whowechina/ju_pico/Production/3DPrint/ju_pico+_button_seat_55.6mm.stl

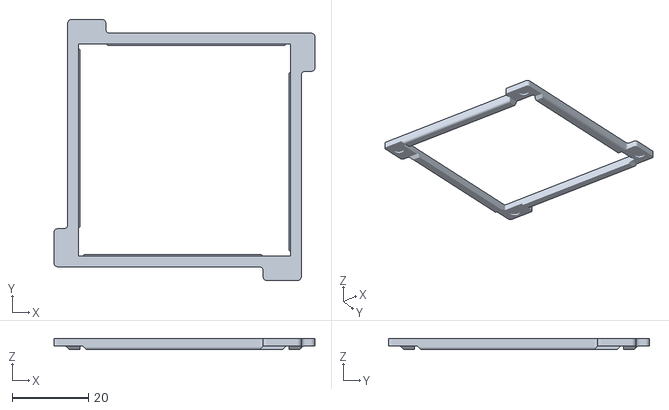
[picture p31: CAD file, 2026-01-03]
Production/3DPrint/ju_pico+_button_seat_55.6mm.stl
68.4 x 68.4 x 3.00
