whowechina/ju_pico/Production/CNC/ju_pico_cnc_banner.step

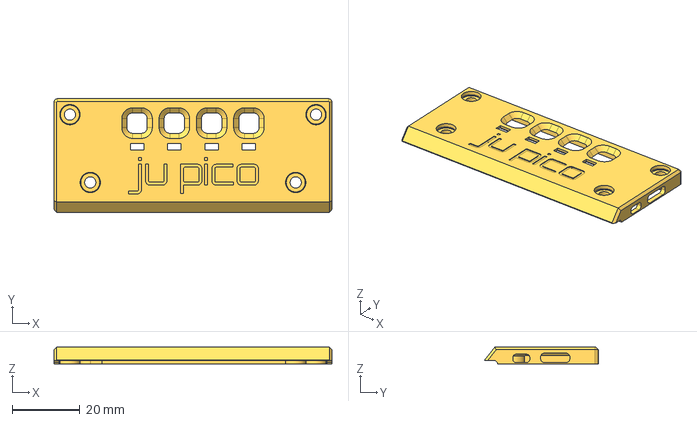
[picture p32: CAD file, 2024-12-04]
Production/CNC/ju_pico_cnc_banner.step
82.0 x 33.5 x 5.00 mm
