whowechina/ju_pico/PCB/Touch/3dmodels/Kailh LP Choc PC Keycap.step

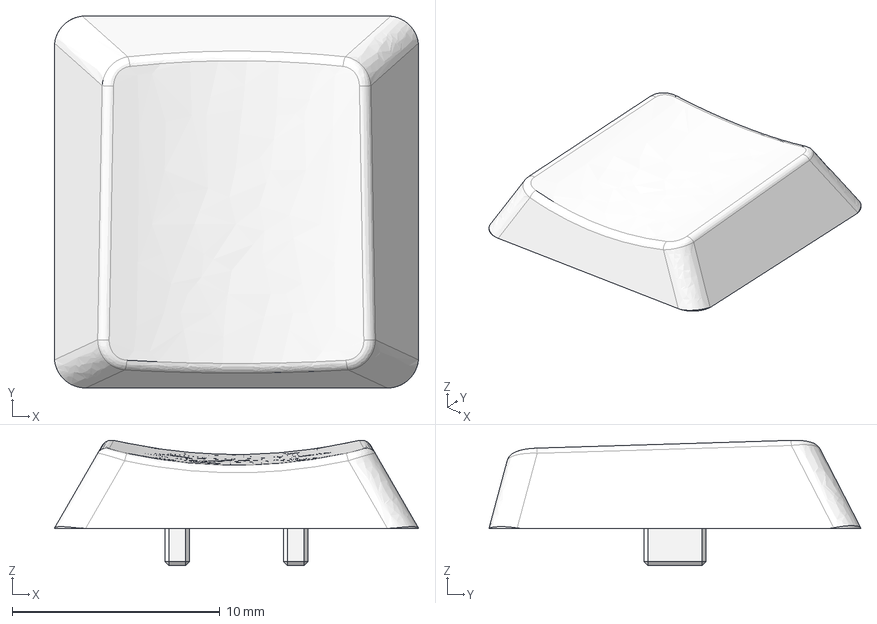
[picture p33: CAD file, 2024-10-23]
PCB/Touch/3dmodels/Kailh LP Choc PC Keycap.step
17.5 x 17.9 x 6.03 mm
