whowechina/ju_pico/PCB/Touch/3dmodels/User Library-WS2812-4020.step

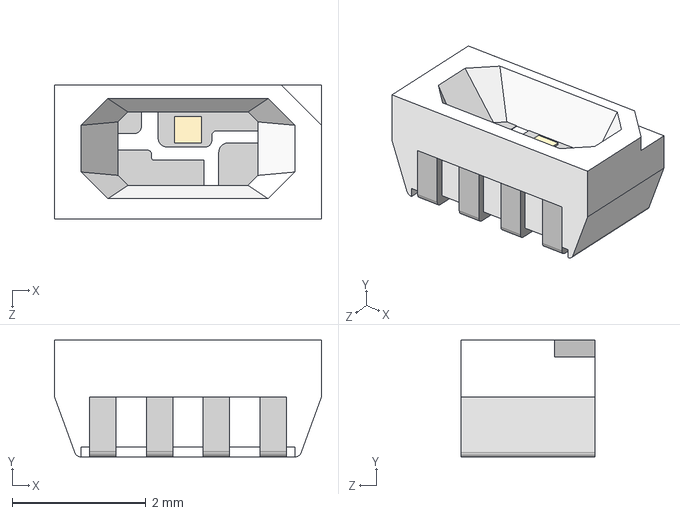
[picture p34: CAD file, 2024-10-23]
PCB/Touch/3dmodels/User Library-WS2812-4020.step
4.00 x 1.75 x 2.00 mm
