whowechina/ju_pico/PCB/Touch/3dmodels/Magnetic Pogo Connector 5 Pin (Type 4).STEP

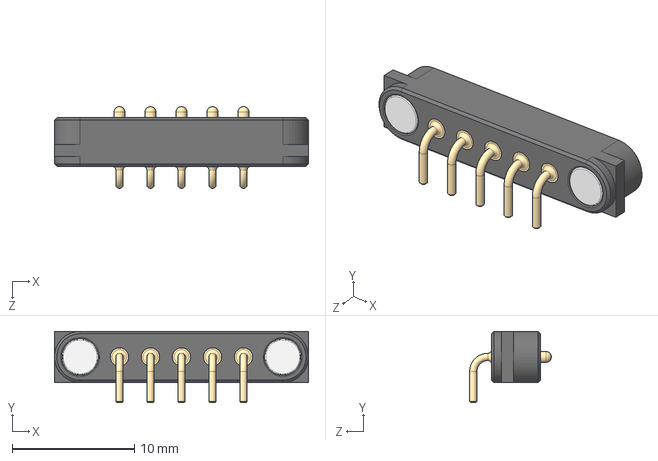
[picture p35: CAD file, 2024-10-23]
PCB/Touch/3dmodels/Magnetic Pogo Connector 5 Pin (Type 4).STEP
20.8 x 5.85 x 6.70 mm
