whowechina/ju_pico/PCB/Touch/3dmodels/Tact Switch 4.5mm SMT.step

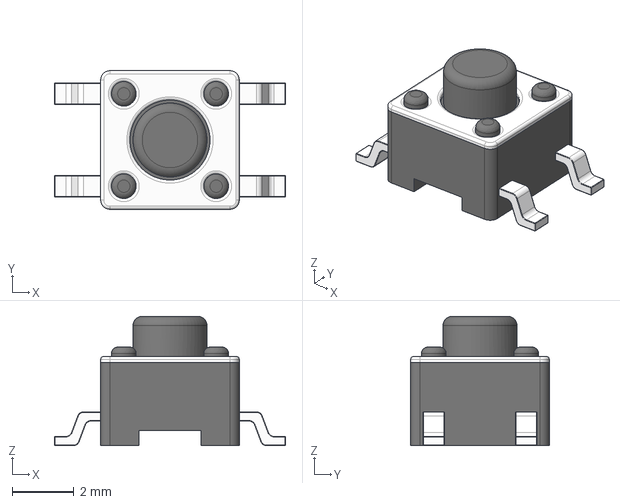
[picture p36: CAD file, 2024-10-23]
PCB/Touch/3dmodels/Tact Switch 4.5mm SMT.step
7.50 x 4.50 x 4.20 mm
