whowechina/ju_pico/PCB/Touch/3dmodels/User Library-pj-393-8.STEP

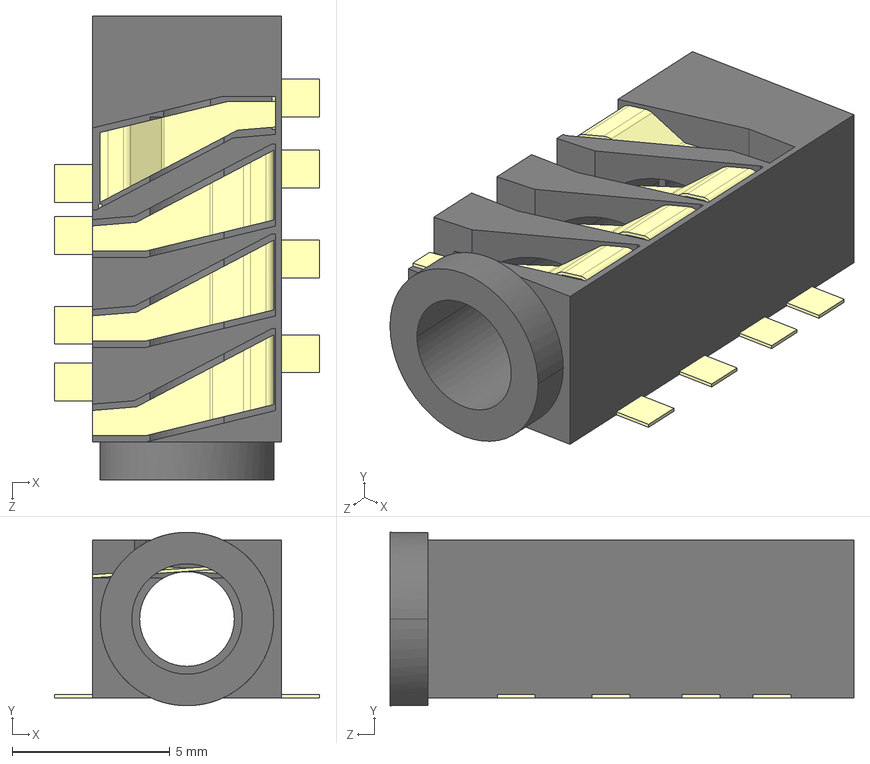
[picture p37: CAD file, 2024-10-23]
PCB/Touch/3dmodels/User Library-pj-393-8.STEP
8.40 x 5.50 x 14.7 mm
PJ-393-8_1
PJ-393-8_2 x 4
PJ-393-8_3
PJ-393-8_4 x 3
