whowechina/ju_pico/Production/3DPrint/ju_pico+_banner.3mf

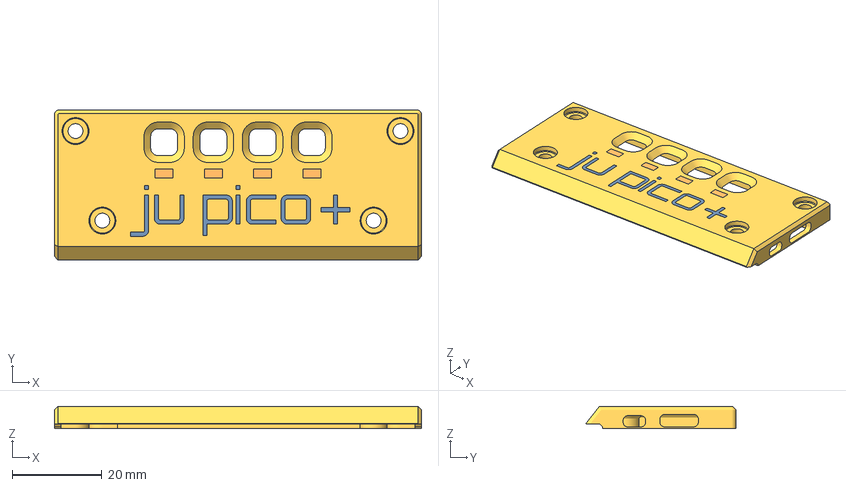
[picture p38: CAD file, 2026-01-03]
Production/3DPrint/ju_pico+_banner.3mf
82.0 x 33.5 x 5.00 mm
Banner
Logo_1
Logo_2
Logo_3
Logo_4
Logo_5
Logo_6
Logo_7
Logo_8
Logo_9
LED_1
LED_2
LED_3
LED_4
