whowechina/ju_pico/PCB/Touch/3dmodels/WS2812-2020.STEP

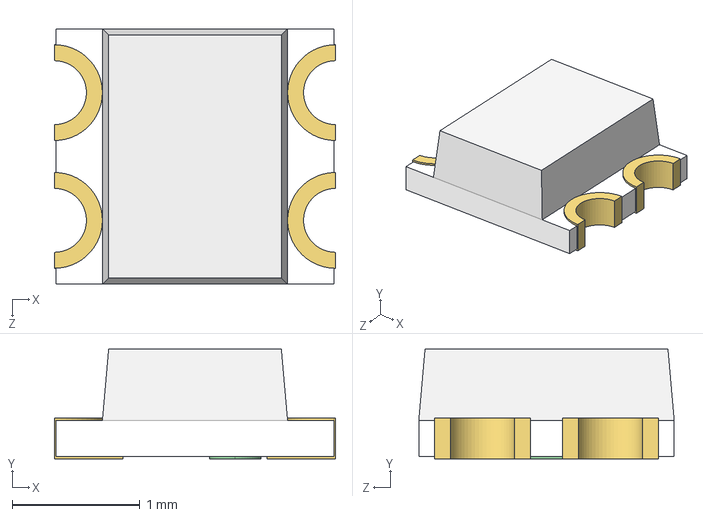
[picture p39: CAD file, 2024-10-23]
PCB/Touch/3dmodels/WS2812-2020.STEP
2.20 x 0.86 x 2.00 mm
