whowechina/ju_pico/Production/3DPrint/ju_pico_led_diffuser_for_cnc.stl

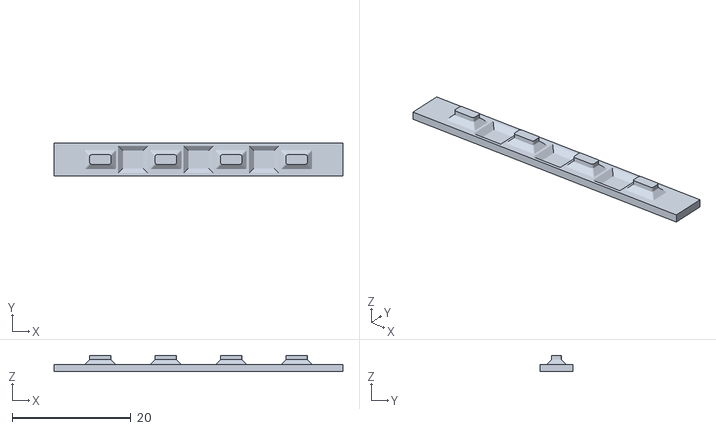
[picture p40: CAD file, 2024-12-06]
Production/3DPrint/ju_pico_led_diffuser_for_cnc.stl
48.6 x 5.60 x 2.70
