whowechina/ju_pico/PCB/Touch/3dmodels/User Library-WS2812-2020.step

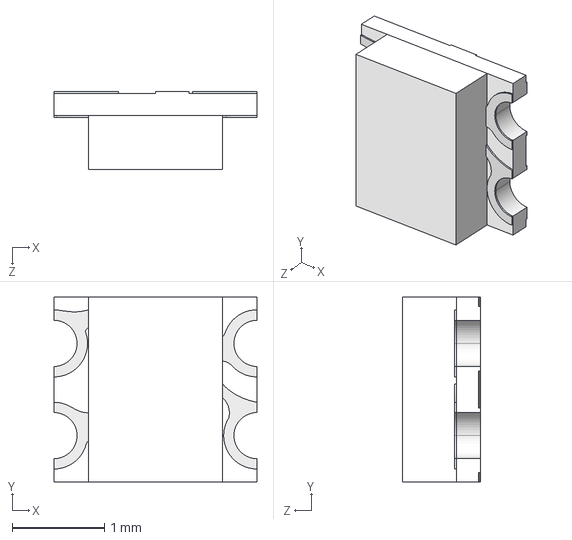
[picture p41: CAD file, 2024-10-23]
PCB/Touch/3dmodels/User Library-WS2812-2020.step
2.20 x 2.00 x 0.84 mm
