whowechina/ju_pico/Production/3DPrint/ju_pico_frame_hexnut.stl

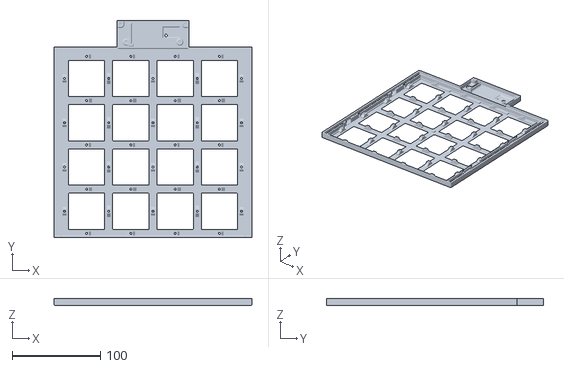
[picture p42: CAD file, 2024-12-04]
Production/3DPrint/ju_pico_frame_hexnut.stl
224.0 x 246.0 x 8.20
