whowechina/ju_pico/PCB/Touch/3dmodels/User Library-PTS645SL95SMTR92-LFS.STEP

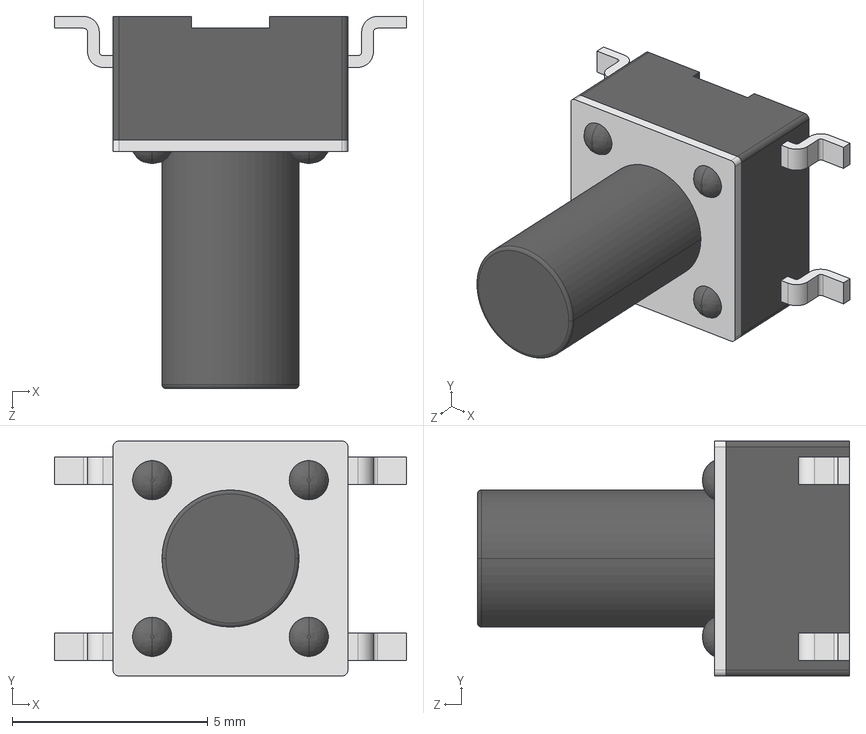
[picture p43: CAD file, 2024-10-23]
PCB/Touch/3dmodels/User Library-PTS645SL95SMTR92-LFS.STEP
9.00 x 6.00 x 9.50 mm
