whowechina/ju_pico/Production/3DPrint/ju_pico_button_seat_39.8mm.stl

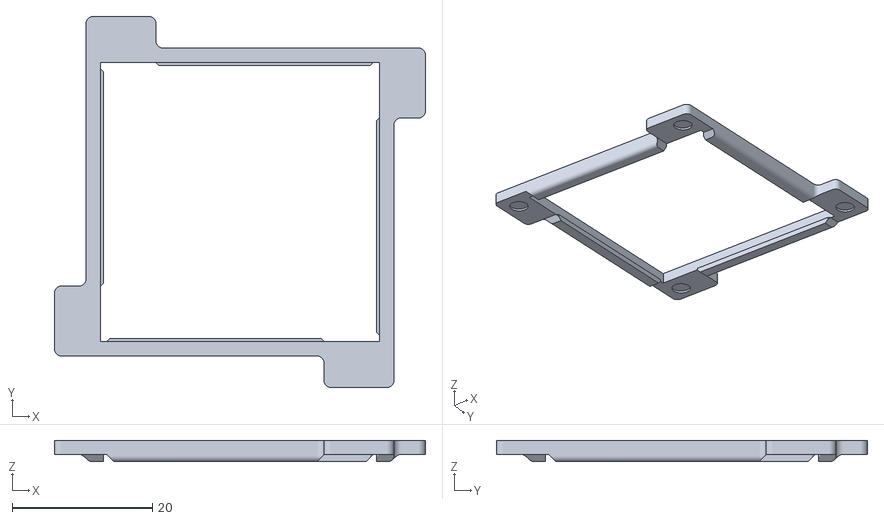
[picture p44: CAD file, 2024-11-11]
Production/3DPrint/ju_pico_button_seat_39.8mm.stl
53.0 x 53.0 x 3.00
