whowechina/ju_pico/PCB/Touch/3dmodels/mpr121_breakout_v13.stl

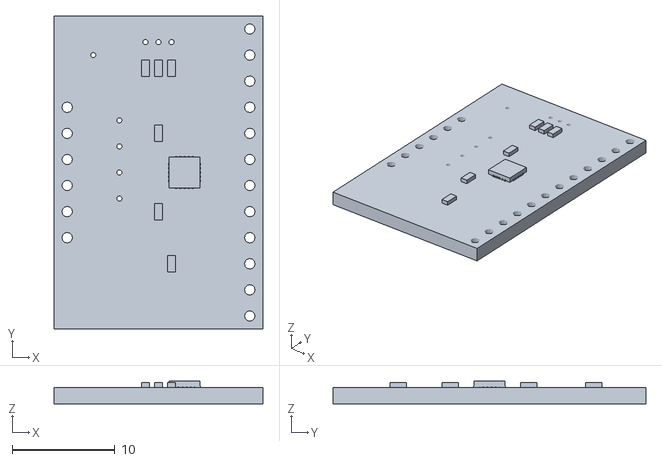
[picture p45: CAD file, 2024-10-23]
PCB/Touch/3dmodels/mpr121_breakout_v13.stl
20.3 x 30.5 x 2.20
