whowechina/ju_pico/PCB/Touch/3dmodels/SW_Kailh_Choc_V1.stp

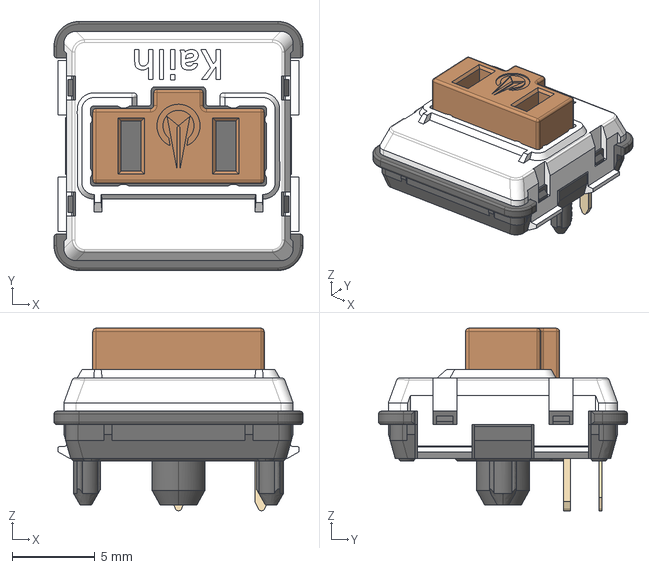
[picture p46: CAD file, 2024-10-23]
PCB/Touch/3dmodels/SW_Kailh_Choc_V1.stp
15.0 x 15.0 x 11.0 mm
