whowechina/ju_pico/PCB/Touch/3dmodels/WS2812B.step

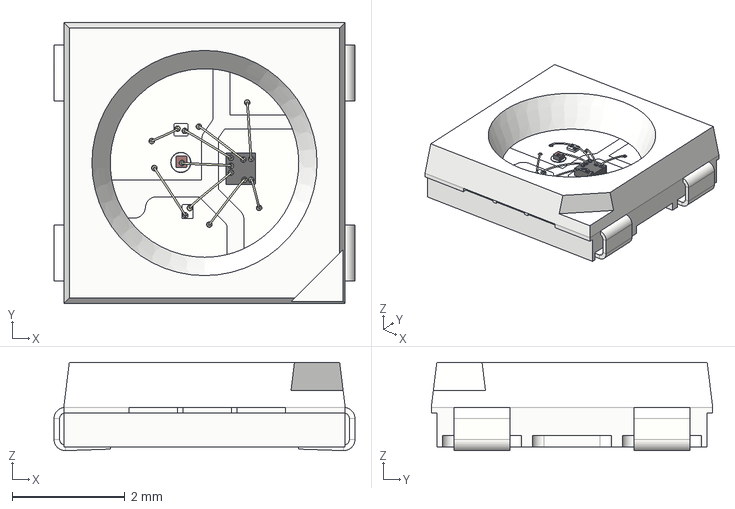
[picture p47: CAD file, 2024-10-23]
PCB/Touch/3dmodels/WS2812B.step
5.35 x 5.00 x 1.57 mm
