whowechina/ju_pico/PCB/Touch/3dmodels/Magnetic Pogo Connector 5 Pin (Type 3).STEP

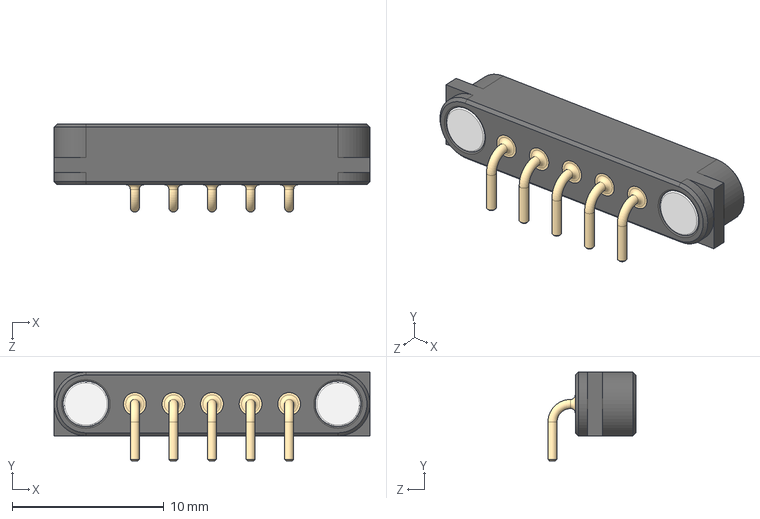
[picture p48: CAD file, 2024-10-23]
PCB/Touch/3dmodels/Magnetic Pogo Connector 5 Pin (Type 3).STEP
20.8 x 5.85 x 5.80 mm
