whowechina/ju_pico/PCB/Touch/3dmodels/EVQ-P1D05M.stp

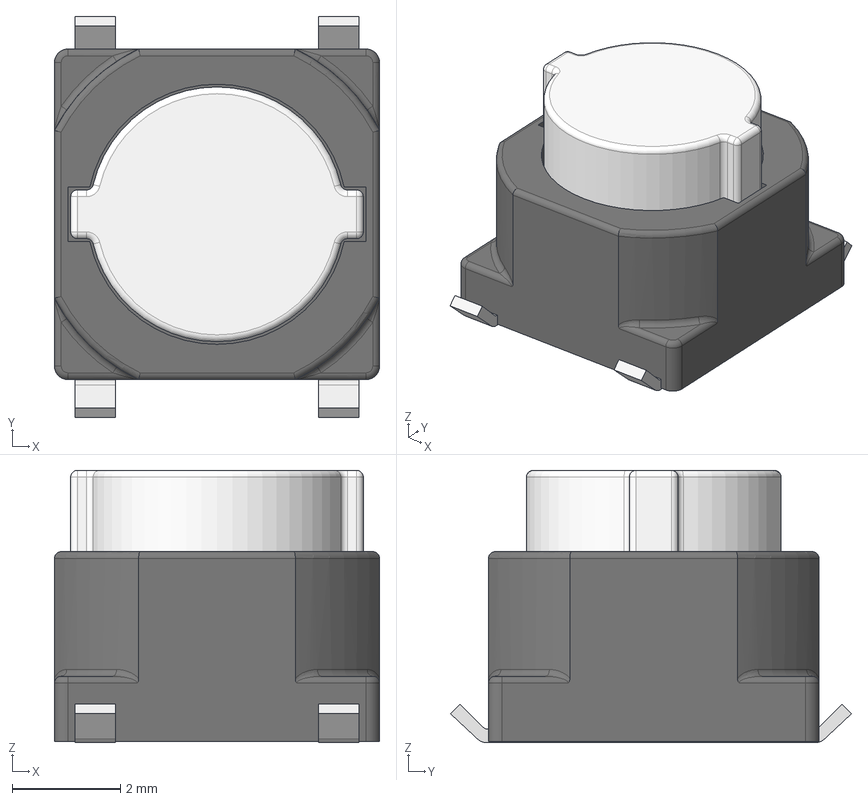
[picture p49: CAD file, 2024-10-23]
PCB/Touch/3dmodels/EVQ-P1D05M.stp
6.00 x 7.40 x 5.03 mm
