whowechina/ju_pico/PCB/Touch/3dmodels/SW_Hotswap_Kailh_MX.stp

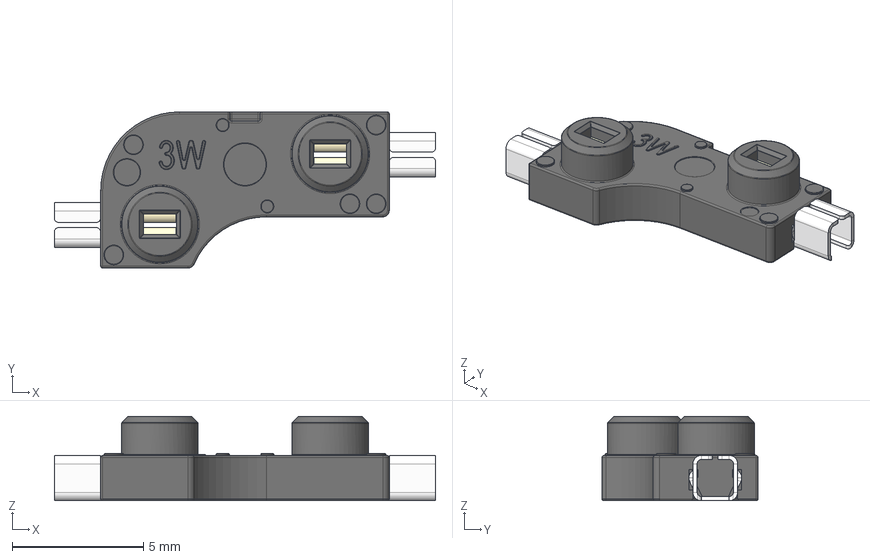
[picture p50: CAD file, 2024-10-23]
PCB/Touch/3dmodels/SW_Hotswap_Kailh_MX.stp
14.5 x 5.95 x 3.22 mm
