whowechina/ju_pico/PCB/Touch/3dmodels/SW_Hotswap_Kailh_Choc_V1.stp

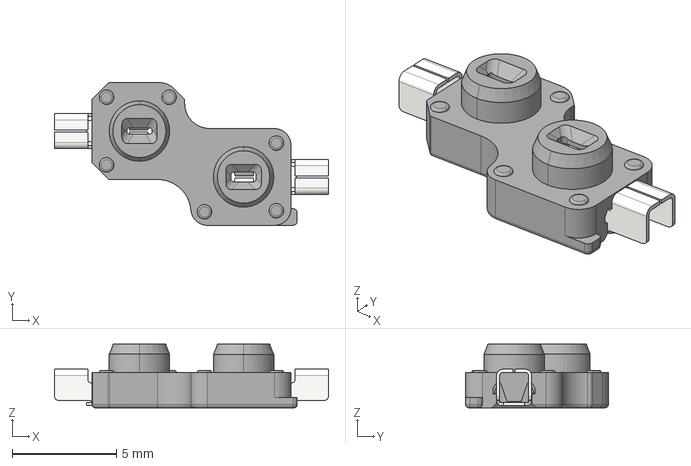
[picture p51: CAD file, 2024-10-23]
PCB/Touch/3dmodels/SW_Hotswap_Kailh_Choc_V1.stp
13.2 x 6.85 x 3.05 mm
