whowechina/ju_pico/PCB/Touch/3dmodels/WS2812-0807.STEP

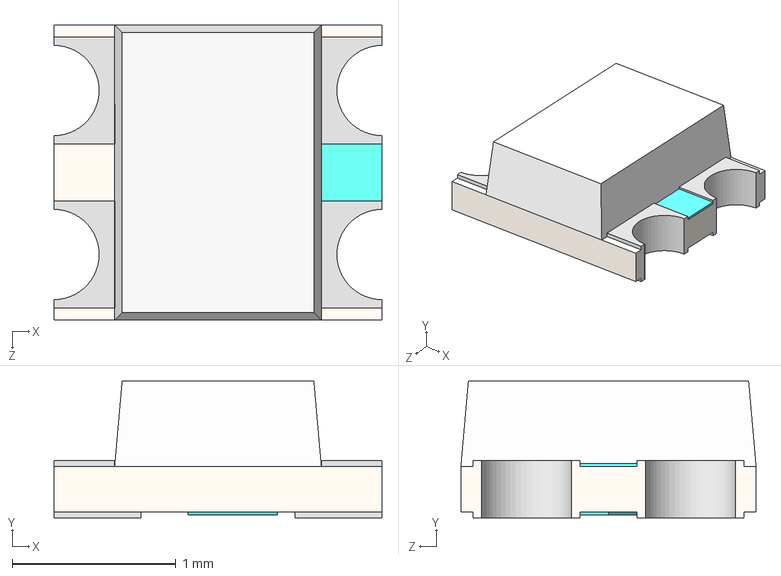
[picture p52: CAD file, 2024-10-23]
PCB/Touch/3dmodels/WS2812-0807.STEP
2.00 x 0.835 x 1.80 mm
