whowechina/ju_pico/PCB/Touch/3dmodels/Magnetic Pogo Connector 5 Pin (Type 1).STEP

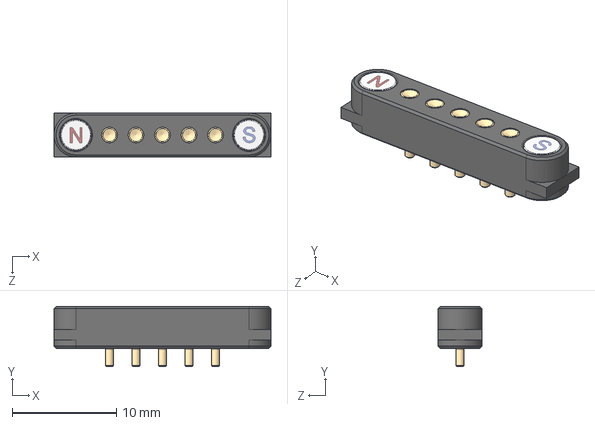
[picture p53: CAD file, 2024-10-23]
PCB/Touch/3dmodels/Magnetic Pogo Connector 5 Pin (Type 1).STEP
20.8 x 5.75 x 4.20 mm
