whowechina/ju_pico/PCB/Touch/3dmodels/SMD WS2812B-3535.step

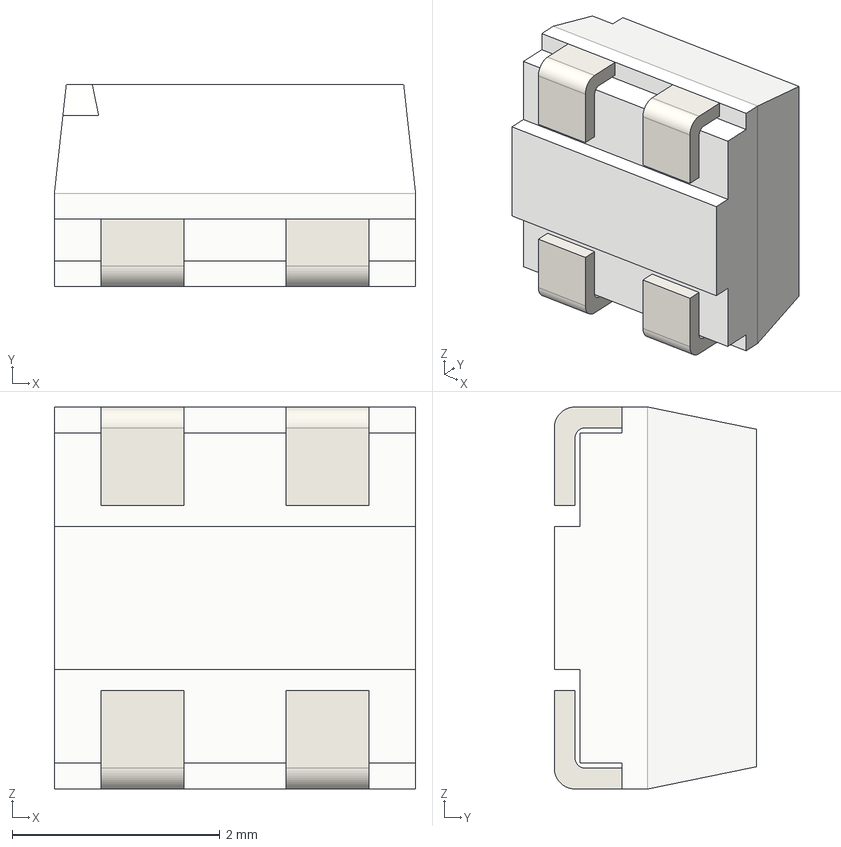
[picture p54: CAD file, 2024-10-23]
PCB/Touch/3dmodels/SMD WS2812B-3535.step
3.48 x 1.95 x 3.68 mm
