whowechina/ju_pico/PCB/Touch/3dmodels/SKPMAM.STEP

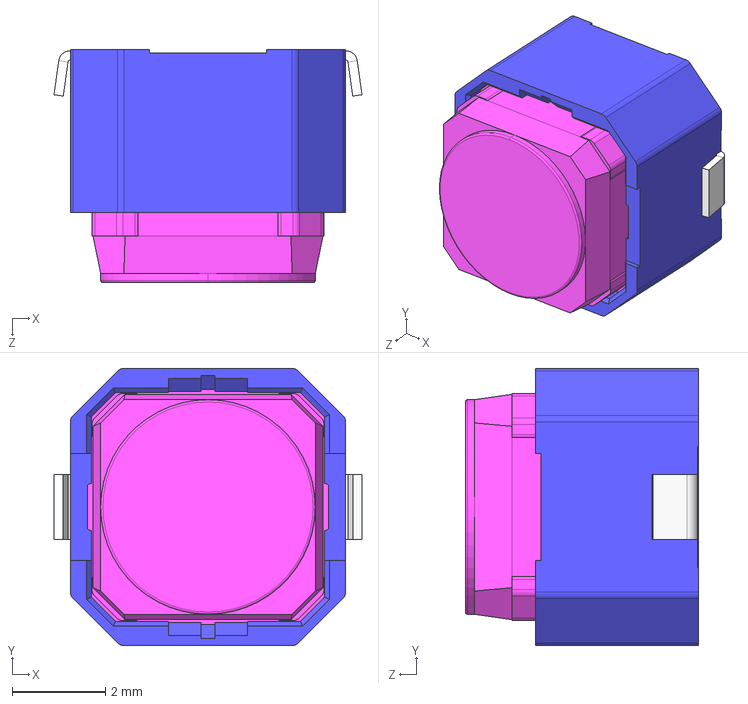
[picture p55: CAD file, 2024-10-23]
PCB/Touch/3dmodels/SKPMAM.STEP
6.60 x 5.94 x 5.00 mm
