whowechina/ju_pico/Matrix/firmware/src/res/marker13/mk0002_flower.h

#ifndef MK0002_FLOWER_C8_A8_H
#define MK0002_FLOWER_C8_A8_H

#include <stdint.h>

/* Marker definition macro */
#define DEF_mk0002_flower_c8_a8 { \
    .fps = 60, \
    { \
        { 8, 8, 13, 32, mk0002_flower_approach_pal8, mk0002_flower_approach_a8, .img8 = mk0002_flower_approach_pix8 }, \
        { 8, 8, 13, 32, mk0002_flower_perfect_pal8, mk0002_flower_perfect_a8, .img8 = mk0002_flower_perfect_pix8 }, \
        { 8, 8, 13, 32, mk0002_flower_great_pal8, mk0002_flower_great_a8, .img8 = mk0002_flower_great_pix8 }, \
        { 8, 8, 13, 32, mk0002_flower_good_pal8, mk0002_flower_good_a8, .img8 = mk0002_flower_good_pix8 }, \
        { 8, 8, 13, 32, mk0002_flower_poor_pal8, mk0002_flower_poor_a8, .img8 = mk0002_flower_poor_pix8 }, \
        { 8, 8, 13, 16, mk0002_flower_miss_pal8, mk0002_flower_miss_a8, .img8 = mk0002_flower_miss_pix8 } \
    } \
}

/* APPROACH - Using 8-bit color depth with 8-bit alpha */
const uint32_t mk0002_flower_approach_pal8[] = {
    0xa7a497, 0x979b66, 0xeb625e, 0xdae39d, 0x68a156, 0x276015, 0xd8e0dd, 0xdaa59c,
    0xdda16b, 0x5d6926, 0x9c7662, 0x6b9624, 0xf0d471, 0xea7836, 0xe98c33, 0xb8dcab,
    0xe27586, 0x153200, 0xa4cc6f, 0x21941f, 0xab7192, 0xbfbfff, 0xe29be2, 0xec0020,
    0x7f0000, 0x687859, 0xb6daff, 0x3f3f7f, 0x007f7f, 0x3c8b42, 0x7f007f, 0x7fbfbf,
    0x7fff7f, 0x7fffff, 0x993366, 0xaaaa00, 0xa9a9a9, 0x000000, 0xfcfcfa, 0x7f7f7f,
    0xaaaa55, 0xfaf9e8, 0xf7f8d8, 0xf4eae6, 0xbcbcbc, 0xf6e7d7, 0xf8f8c8, 0xe9d7d6,
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
    0x36, 0xad, 0xcd, 0xbb, 0xe0, 0xe5, 0xe1, 0xe0, 0xdd, 0xda, 0xde, 0x55, 0x08,
    0x35, 0x46, 0x46, 0x57, 0x8b, 0x9c, 0xd1, 0xc8, 0xcd, 0x97, 0x3e, 0x04, 0x03,
    0x00, 0x00, 0x0b, 0x78, 0xa3, 0x69, 0x55, 0x77, 0x74, 0x4e, 0x36, 0x1b, 0x1c,
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
};

#endif // MK0002_FLOWER_C8_A8_H
