whowechina/ju_pico/Matrix/firmware/src/res/marker13/trail13.h

#ifndef TRAIL13_C4_A4_H
#define TRAIL13_C4_A4_H

#include <stdint.h>

/* Trail definition macro */
#define DEF_trail13_c4_a4 { \
    .stem = { 4, 4, 13, 15, trail13_stem_pal4, trail13_stem_a4, .img8 = trail13_stem_pix4 }, \
    .marker_off = { 4, 4, 13, 16, trail13_marker_off_pal4, trail13_marker_off_a4, .img8 = trail13_marker_off_pix4 }, \
    .marker_on = { 4, 4, 13, 16, trail13_marker_on_pal4, trail13_marker_on_a4, .img8 = trail13_marker_on_pix4 }, \
    .marker_glow = { 4, 4, 13, 16, trail13_marker_glow_pal4, trail13_marker_glow_a4, .img8 = trail13_marker_glow_pix4 }, \
    .arrow_tail = { 4, 4, 13, 16, trail13_arrow_tail_pal4, trail13_arrow_tail_a4, .img8 = trail13_arrow_tail_pix4 }, \
    .arrow = { 4, 4, 13, 16, trail13_arrow_pal4, trail13_arrow_a4, .img8 = trail13_arrow_pix4 }, \
    .arrow_grow = { 4, 4, 13, 8, trail13_arrow_grow_pal4, trail13_arrow_grow_a4, .img8 = trail13_arrow_grow_pix4 } \
}

/* STEM - Using 4-bit color depth with 4-bit alpha */
const uint32_t trail13_stem_pal4[] = {
    0xffffff, 0xc4e3ff, 0x9cd3ff, 0x000000, 0x000000, 0x000000, 0x000000, 0x000000,
    0x000000, 0x000000, 0x000000, 0x000000, 0x000000, 0x000000, 0x000000, 0x000000
};

const uint8_t trail13_stem_pix4[] = {
    0x33, 0x30, 0x32, 0x12, 0x30, 0x33, 0x33, 0x33, 0x03, 0x21, 0x23, 0x03, 0x33,
    0x33, 0x30, 0x32, 0x12, 0x30, 0x33, 0x33, 0x33, 0x03, 0x21, 0x23, 0x03, 0x33,
    0x33, 0x30, 0x32, 0x12, 0x30, 0x33, 0x33, 0x33, 0x03, 0x21, 0x23, 0x03, 0x33,
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
    0x00, 0x0a, 0xff, 0xff, 0xfa, 0x00, 0x00, 0x00, 0x2f, 0xff, 0xff, 0x20, 0x00,
    0x00, 0x00, 0xaf, 0xff, 0xa0, 0x00, 0x00, 0x00, 0x02, 0xff, 0xf3, 0x00, 0x00,
    0x00, 0x00, 0x0a, 0xfb, 0x00, 0x00, 0x00, 0x00, 0x00, 0x5f, 0x50, 0x00, 0x00,
    0x00, 0x00, 0x04, 0xe4, 0x00, 0x00, 0x09, 0xff, 0xff, 0xff, 0xff, 0xff, 0xfa,
    0x2f, 0xff, 0xff, 0xff, 0xff, 0xff, 0x30, 0x9f, 0xff, 0xff, 0xff, 0xff, 0xa0,
    0x02, 0xff, 0xff, 0xff, 0xff, 0xf2, 0x00, 0x09, 0xff, 0xff, 0xff, 0xfa, 0x00,
    0x00, 0x2f, 0xff, 0xff, 0xff, 0x30, 0x00, 0x00, 0xaf, 0xff, 0xff, 0xa0, 0x00,
    0x00, 0x02, 0xff, 0xff, 0xf2, 0x00, 0x00, 0x00, 0x0a, 0xff, 0xfa, 0x00, 0x00,
    0x00, 0x00, 0x2f, 0xff, 0x30, 0x00, 0x00, 0x00, 0x00, 0xaf, 0xb0, 0x00, 0x00,
    0x00, 0x00, 0x05, 0xf5, 0x00, 0x00, 0x00, 0x00, 0x00, 0x4e, 0x40, 0x00, 0x00,
    0x9f, 0xff, 0xff, 0xff, 0xff, 0xff, 0xa2, 0xff, 0xff, 0xff, 0xff, 0xff, 0xf3,
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
};

#endif // TRAIL13_C4_A4_H
