whowechina/ju_pico/Matrix/firmware/src/res/marker13/mk0001_cyber.h

#ifndef MK0001_CYBER_C8_A8_H
#define MK0001_CYBER_C8_A8_H

#include <stdint.h>

/* Marker definition macro */
#define DEF_mk0001_cyber_c8_a8 { \
    .fps = 60, \
    { \
        { 8, 8, 13, 32, mk0001_cyber_approach_pal8, mk0001_cyber_approach_a8, .img8 = mk0001_cyber_approach_pix8 }, \
        { 8, 8, 13, 32, mk0001_cyber_perfect_pal8, mk0001_cyber_perfect_a8, .img8 = mk0001_cyber_perfect_pix8 }, \
        { 8, 8, 13, 32, mk0001_cyber_great_pal8, mk0001_cyber_great_a8, .img8 = mk0001_cyber_great_pix8 }, \
        { 8, 8, 13, 32, mk0001_cyber_good_pal8, mk0001_cyber_good_a8, .img8 = mk0001_cyber_good_pix8 }, \
        { 8, 8, 13, 32, mk0001_cyber_poor_pal8, mk0001_cyber_poor_a8, .img8 = mk0001_cyber_poor_pix8 }, \
        { 8, 8, 13, 16, mk0001_cyber_miss_pal8, mk0001_cyber_miss_a8, .img8 = mk0001_cyber_miss_pix8 } \
    } \
}

/* APPROACH - Using 8-bit color depth with 8-bit alpha */
const uint32_t mk0001_cyber_approach_pal8[] = {
    0x64a059, 0x6b6461, 0x25e118, 0x9b656e, 0xe1199e, 0x52df24, 0x2ba318, 0xd15f99,
    0x9b9263, 0xa96a97, 0xa48fa0, 0xa61b94, 0xe326d2, 0xdb6973, 0x63dd55, 0x57a628,
    0xdc8660, 0xe85ed6, 0x9a246d, 0xd58898, 0xfb0f5e, 0x28da56, 0x7c5b82, 0x6f2773,
    0x9dec9d, 0xec9ae3, 0x93ff6a, 0x487c2f, 0x00ffff, 0x7a8982, 0xff0039, 0x0000ff,
    0x550000, 0x2a0055, 0x3f7f31, 0x369345, 0x7a3384, 0x7f00ff, 0xb60024, 0xffff99,
    0x000000, 0x03fe01, 0x28fd05, 0xfe00fc, 0xfd03c9, 0xfd03d5, 0x17fd03, 0xfb08e8,
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
    0xb4, 0x84, 0x0c, 0x34, 0x80, 0xac, 0xab, 0x75, 0x55, 0x02, 0x02, 0x2d, 0x12,
    0x83, 0x0a, 0x67, 0xb9, 0x91, 0x84, 0x9c, 0xa5, 0xbc, 0xa1, 0x2b, 0x00, 0x28,
    0x0a, 0x58, 0xa6, 0x6a, 0x54, 0x66, 0x7c, 0x71, 0x52, 0x94, 0xbb, 0x2e, 0x01,
    0x2d, 0xb3, 0x3d, 0x4e, 0xaf, 0xb1, 0xd3, 0xdf, 0xa0, 0x47, 0x98, 0xa9, 0x14,
    0x86, 0xa8, 0x40, 0xaf, 0xb1, 0xb4, 0xcb, 0xd6, 0xbb, 0x7f, 0x83, 0xbd, 0x8d,
    0xc8, 0xd5, 0xcc, 0xeb, 0xd7, 0xb9, 0xd0, 0xe4, 0xec, 0xd6, 0xc9, 0xda, 0xdd,
    0xa9, 0xd4, 0xc6, 0xe8, 0xed, 0xe7, 0xf0, 0xeb, 0xd9, 0xff, 0xf4, 0xdb, 0xc8,
    0x51, 0x8d, 0x95, 0xe3, 0xda, 0xde, 0xdf, 0xdf, 0xe0, 0xf4, 0xd6, 0xca, 0xaa,
    0x34, 0x18, 0x35, 0x91, 0x96, 0xb0, 0xba, 0xca, 0xe0, 0xd6, 0xa3, 0x81, 0x74,
    0x1e, 0x35, 0x5c, 0x9e, 0x79, 0x61, 0x9e, 0xce, 0xe9, 0xbd, 0x9b, 0x6b, 0x97,
    0x00, 0x3e, 0x60, 0x8d, 0x95, 0x95, 0x92, 0xaa, 0xc6, 0xbb, 0x73, 0x7c, 0xb0,
    0x26, 0x10, 0x3c, 0x9a, 0x98, 0x90, 0x85, 0x77, 0x67, 0x6c, 0x86, 0xad, 0xab,
    0xaa, 0x40, 0x00, 0x3c, 0x84, 0x9f, 0x72, 0x3c, 0x60, 0x8f, 0xaf, 0xab, 0x5d,
    0xa2, 0x76, 0x0b, 0x2a, 0x75, 0xa6, 0x97, 0x60, 0x42, 0x00, 0x05, 0x28, 0x10,
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
};

#endif // MK0001_CYBER_C8_A8_H
