whowechina/ju_pico/Matrix/firmware/src/res/marker13/mk0003_afro.h

#ifndef MK0003_AFRO_C8_A8_H
#define MK0003_AFRO_C8_A8_H

#include <stdint.h>

/* Marker definition macro */
#define DEF_mk0003_afro_c8_a8 { \
    .fps = 60, \
    { \
        { 8, 8, 13, 32, mk0003_afro_approach_pal8, mk0003_afro_approach_a8, .img8 = mk0003_afro_approach_pix8 }, \
        { 8, 8, 13, 32, mk0003_afro_perfect_pal8, mk0003_afro_perfect_a8, .img8 = mk0003_afro_perfect_pix8 }, \
        { 8, 8, 13, 32, mk0003_afro_great_pal8, mk0003_afro_great_a8, .img8 = mk0003_afro_great_pix8 }, \
        { 8, 8, 13, 32, mk0003_afro_good_pal8, mk0003_afro_good_a8, .img8 = mk0003_afro_good_pix8 }, \
        { 8, 8, 13, 32, mk0003_afro_poor_pal8, mk0003_afro_poor_a8, .img8 = mk0003_afro_poor_pix8 }, \
        { 8, 8, 13, 16, mk0003_afro_miss_pal8, mk0003_afro_miss_a8, .img8 = mk0003_afro_miss_pix8 } \
    } \
}

/* APPROACH - Using 8-bit color depth with 8-bit alpha */
const uint32_t mk0003_afro_approach_pal8[] = {
    0x000000, 0xfffefe, 0xfefe00, 0xfe8400, 0xfea801, 0xfdb701, 0xfe7c00, 0xfdc700,
    0xfe9701, 0xfed600, 0xfee700, 0xfef9e9, 0xff0000, 0xfe5500, 0xffbf7f, 0xfe6a00,
    0xffd57f, 0xffd3a9, 0xffbf3f, 0xfff6dd, 0xffeedd, 0xffe7b5, 0xffcc66, 0xffdb95,
    0xffaa55, 0xff8b19, 0xffd455, 0xff6611, 0xff007f, 0xffebc5, 0xff4800, 0xffffaa,
    0xffcc99, 0xff3f00, 0xffe7e2, 0xff7f3f, 0xffff7f, 0xffaaaa, 0xffdab6, 0xffda6d,
    0xecdab6, 0xff7f7f, 0xffff3f, 0xdab691, 0xffff55, 0xffff66, 0xffcc33, 0xff002a,
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
    0x14, 0x3a, 0x1c, 0x2c, 0x2e, 0x1b, 0x3a, 0x1b, 0x31, 0x2a, 0x1e, 0x3a, 0x12,
    0x39, 0x0b, 0x52, 0x27, 0x21, 0x57, 0x09, 0x5a, 0x1b, 0x2e, 0x4d, 0x0d, 0x38,
    0x1c, 0x36, 0x27, 0x2f, 0x30, 0x25, 0x34, 0x28, 0x32, 0x2c, 0x29, 0x32, 0x15,
    0x00, 0x00, 0x00, 0x00, 0x00, 0x00, 0x00, 0x00, 0x00, 0x00, 0x00, 0x0b, 0x09,
    0x1f, 0x35, 0x62, 0x5d, 0x60, 0x81, 0x86, 0x53, 0x5f, 0x6d, 0x74, 0x68, 0x3c,
    0x78, 0x93, 0xc7, 0xb2, 0xc2, 0xc6, 0xce, 0xc3, 0xbc, 0x8e, 0xea, 0x6f, 0x33,
    0x35, 0x70, 0xa1, 0x85, 0x9f, 0xbd, 0xb2, 0xc4, 0x62, 0x4b, 0xdd, 0x75, 0x3c,
    0x31, 0x8f, 0xa9, 0x82, 0xce, 0xc1, 0xc7, 0xc0, 0xc6, 0xc0, 0xb1, 0xaf, 0x38,
    0x67, 0x6a, 0x25, 0x34, 0x3b, 0x39, 0x5e, 0x33, 0x3b, 0x47, 0x45, 0x6b, 0x67,
    0x0b, 0x00, 0x00, 0x00, 0x00, 0x00, 0x00, 0x00, 0x00, 0x00, 0x00, 0x00, 0x11,
    0x00, 0x00, 0x03, 0x04, 0x05, 0x03, 0x05, 0x03, 0x05, 0x04, 0x04, 0x00, 0x00,
    0x0e, 0x24, 0x38, 0x3e, 0x30, 0x41, 0x2e, 0x42, 0x30, 0x3f, 0x37, 0x25, 0x0e,
    0x3d, 0x43, 0x52, 0x39, 0x45, 0x4d, 0x33, 0x50, 0x43, 0x3a, 0x52, 0x41, 0x3f,
    0x0c, 0x30, 0x16, 0x22, 0x27, 0x14, 0x30, 0x13, 0x29, 0x20, 0x18, 0x30, 0x0a,
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
};

#endif // MK0003_AFRO_C8_A8_H
