whowechina/ju_pico/Matrix/firmware/src/res/marker13/mk0004_shutter.h

#ifndef MK0004_SHUTTER_C8_A8_H
#define MK0004_SHUTTER_C8_A8_H

#include <stdint.h>

/* Marker definition macro */
#define DEF_mk0004_shutter_c8_a8 { \
    .fps = 60, \
    { \
        { 8, 8, 13, 32, mk0004_shutter_approach_pal8, mk0004_shutter_approach_a8, .img8 = mk0004_shutter_approach_pix8 }, \
        { 8, 8, 13, 32, mk0004_shutter_perfect_pal8, mk0004_shutter_perfect_a8, .img8 = mk0004_shutter_perfect_pix8 }, \
        { 8, 8, 13, 32, mk0004_shutter_great_pal8, mk0004_shutter_great_a8, .img8 = mk0004_shutter_great_pix8 }, \
        { 8, 8, 13, 32, mk0004_shutter_good_pal8, mk0004_shutter_good_a8, .img8 = mk0004_shutter_good_pix8 }, \
        { 8, 8, 13, 32, mk0004_shutter_poor_pal8, mk0004_shutter_poor_a8, .img8 = mk0004_shutter_poor_pix8 }, \
        { 8, 8, 13, 16, mk0004_shutter_miss_pal8, mk0004_shutter_miss_a8, .img8 = mk0004_shutter_miss_pix8 } \
    } \
}

/* APPROACH - Using 8-bit color depth with 8-bit alpha */
const uint32_t mk0004_shutter_approach_pal8[] = {
    0xe09a64, 0xefe4d3, 0xdfad9c, 0xefdda1, 0xa05a1e, 0xe6d778, 0xa59d96, 0xa26956,
    0xdb731f, 0x5c5532, 0xdb8239, 0x2d1f20, 0xa69868, 0x66360f, 0x2f3b40, 0x696995,
    0x614f58, 0xa8863c, 0xaaffff, 0x7f949f, 0x7fb2cc, 0x813d0f, 0x89b0c4, 0xbfc0bf,
    0xd47f55, 0x000000, 0x775947, 0x865736, 0x573827, 0x977865, 0x774828, 0x675547,
    0x876856, 0x574537, 0x674936, 0x786557, 0x795438, 0x886448, 0x975527, 0x3a3a39,
    0x472916, 0x997559, 0x956846, 0x694429, 0x754b34, 0x574c44, 0x464745, 0x585755,
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
    0xfe, 0xff, 0xff, 0xff, 0xfe, 0xff, 0xed, 0xc3, 0xbc, 0xc0, 0xb8, 0xae, 0xa3,
    0xfd, 0xfe, 0xfe, 0xfe, 0xfd, 0xff, 0xe3, 0xc0, 0xc0, 0xba, 0xbb, 0xb8, 0xa1,
    0xc5, 0xc8, 0xc9, 0xcb, 0xce, 0xc6, 0xd4, 0xff, 0xfd, 0xfe, 0xfe, 0xfe, 0xfd,
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
};

#endif // MK0004_SHUTTER_C8_A8_H
