whowechina/ju_pico/Matrix/firmware/src/res/marker13/mk0005_blue_ring.h

#ifndef MK0005_BLUE_RING_C8_A8_H
#define MK0005_BLUE_RING_C8_A8_H

#include <stdint.h>

/* Marker definition macro */
#define DEF_mk0005_blue_ring_c8_a8 { \
    .fps = 60, \
    { \
        { 8, 8, 13, 32, mk0005_blue_ring_approach_pal8, mk0005_blue_ring_approach_a8, .img8 = mk0005_blue_ring_approach_pix8 }, \
        { 8, 8, 13, 32, mk0005_blue_ring_perfect_pal8, mk0005_blue_ring_perfect_a8, .img8 = mk0005_blue_ring_perfect_pix8 }, \
        { 8, 8, 13, 32, mk0005_blue_ring_great_pal8, mk0005_blue_ring_great_a8, .img8 = mk0005_blue_ring_great_pix8 }, \
        { 8, 8, 13, 32, mk0005_blue_ring_good_pal8, mk0005_blue_ring_good_a8, .img8 = mk0005_blue_ring_good_pix8 }, \
        { 8, 8, 13, 32, mk0005_blue_ring_poor_pal8, mk0005_blue_ring_poor_a8, .img8 = mk0005_blue_ring_poor_pix8 }, \
        { 8, 8, 13, 16, mk0005_blue_ring_miss_pal8, mk0005_blue_ring_miss_a8, .img8 = mk0005_blue_ring_miss_pix8 } \
    } \
}

/* APPROACH - Using 8-bit color depth with 8-bit alpha */
const uint32_t mk0005_blue_ring_approach_pal8[] = {
    0xa4dee1, 0x5fe3e6, 0xa09cda, 0xe297a4, 0xa567d4, 0xdfdee1, 0x20a4ea, 0x24e3e3,
    0x5f94e1, 0xe575a1, 0xa791b5, 0xde5ccb, 0xd192e5, 0xf3e3ad, 0x7365de, 0xae7ab5,
    0xa931c8, 0x00ff95, 0x236ded, 0xff0000, 0x31baba, 0x88c2b8, 0x007f7f, 0x78ada5,
    0xff6161, 0x48c5b0, 0x00ff6d, 0x00ff00, 0xffff00, 0xffff7f, 0x7f7f7f, 0x3333ff,
    0xfefefe, 0x1775fc, 0x000000, 0x01cbca, 0x1585f6, 0x02fcfc, 0x01d7d5, 0xe7fafd,
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
    0x21, 0x62, 0x8e, 0xa3, 0xa8, 0xa7, 0x92, 0x9f, 0xa1, 0x9b, 0x96, 0x64, 0x30,
    0x0e, 0x1a, 0x14, 0x40, 0x7d, 0x94, 0x8a, 0x94, 0x7b, 0x42, 0x15, 0x1b, 0x12,
    0x13, 0x2d, 0x24, 0x49, 0x84, 0x91, 0x86, 0x8f, 0x89, 0x49, 0x27, 0x2e, 0x1b,
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
};

#endif // MK0005_BLUE_RING_C8_A8_H
