whowechina/ju_pico/Matrix/firmware/src/res/marker13/mk0006_fireworks.h

#ifndef MK0006_FIREWORKS_C8_A8_H
#define MK0006_FIREWORKS_C8_A8_H

#include <stdint.h>

/* Marker definition macro */
#define DEF_mk0006_fireworks_c8_a8 { \
    .fps = 60, \
    { \
        { 8, 8, 13, 32, mk0006_fireworks_approach_pal8, mk0006_fireworks_approach_a8, .img8 = mk0006_fireworks_approach_pix8 }, \
        { 8, 8, 13, 32, mk0006_fireworks_perfect_pal8, mk0006_fireworks_perfect_a8, .img8 = mk0006_fireworks_perfect_pix8 }, \
        { 8, 8, 13, 32, mk0006_fireworks_great_pal8, mk0006_fireworks_great_a8, .img8 = mk0006_fireworks_great_pix8 }, \
        { 8, 8, 13, 32, mk0006_fireworks_good_pal8, mk0006_fireworks_good_a8, .img8 = mk0006_fireworks_good_pix8 }, \
        { 8, 8, 13, 32, mk0006_fireworks_poor_pal8, mk0006_fireworks_poor_a8, .img8 = mk0006_fireworks_poor_pix8 }, \
        { 8, 8, 13, 16, mk0006_fireworks_miss_pal8, mk0006_fireworks_miss_a8, .img8 = mk0006_fireworks_miss_pix8 } \
    } \
}

/* APPROACH - Using 8-bit color depth with 8-bit alpha */
const uint32_t mk0006_fireworks_approach_pal8[] = {
    0x030200, 0xb6761d, 0x673900, 0x291801, 0x784301, 0x482903, 0xaa6d1b, 0x985500,
    0x331d01, 0x150a00, 0xc27c1c, 0x583503, 0xca8423, 0x844a01, 0x392303, 0xca821c,
    0xad701c, 0xa35b00, 0xd48b27, 0x713e00, 0x562d02, 0x7a6707, 0x4c3a04, 0x181302,
    0xd3841c, 0xb66401, 0x865702, 0x3a3506, 0x924d00, 0xe2942c, 0xdb902b, 0xc27e20,
    0x544306, 0x674808, 0xaa6301, 0xba7920, 0x785404, 0xa88002, 0x555348, 0x887707,
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
    0xc1, 0xb6, 0xaf, 0xab, 0xaa, 0xaa, 0xaa, 0xaa, 0xaa, 0xab, 0xaf, 0xb6, 0xc1,
    0xc6, 0xc1, 0xbd, 0xbb, 0xbb, 0xbb, 0xbb, 0xbb, 0xbb, 0xbb, 0xbd, 0xc1, 0xc6,
    0xbb, 0xb7, 0xb4, 0xb3, 0xb3, 0xb3, 0xb3, 0xb3, 0xb3, 0xb3, 0xb5, 0xb8, 0xbb,
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
};

#endif // MK0006_FIREWORKS_C8_A8_H
