whowechina/ju_pico/Matrix/firmware/src/res/marker13/mk0007_target.h

#ifndef MK0007_TARGET_C8_A8_H
#define MK0007_TARGET_C8_A8_H

#include <stdint.h>

/* Marker definition macro */
#define DEF_mk0007_target_c8_a8 { \
    .fps = 60, \
    { \
        { 8, 8, 13, 32, mk0007_target_approach_pal8, mk0007_target_approach_a8, .img8 = mk0007_target_approach_pix8 }, \
        { 8, 8, 13, 32, mk0007_target_perfect_pal8, mk0007_target_perfect_a8, .img8 = mk0007_target_perfect_pix8 }, \
        { 8, 8, 13, 32, mk0007_target_great_pal8, mk0007_target_great_a8, .img8 = mk0007_target_great_pix8 }, \
        { 8, 8, 13, 32, mk0007_target_good_pal8, mk0007_target_good_a8, .img8 = mk0007_target_good_pix8 }, \
        { 8, 8, 13, 32, mk0007_target_poor_pal8, mk0007_target_poor_a8, .img8 = mk0007_target_poor_pix8 }, \
        { 8, 8, 13, 16, mk0007_target_miss_pal8, mk0007_target_miss_a8, .img8 = mk0007_target_miss_pix8 } \
    } \
}

/* APPROACH - Using 8-bit color depth with 8-bit alpha */
const uint32_t mk0007_target_approach_pal8[] = {
    0x000000, 0xfeaa41, 0xfea93e, 0xfeb446, 0xffff00, 0xfd983a, 0xff7f00, 0xfc8738,
    0xffaa55, 0xfe0000, 0xfc7935, 0xffb93d, 0xfc5726, 0xffff7e, 0xff7f7f, 0xfb672b,
    0xfc9942, 0xfc4a20, 0xfec54b, 0xfc441e, 0xfd6932, 0xfcc752, 0xfb3b1a, 0xffaa2a,
    0xfcd456, 0xffffff, 0xffaa00, 0xffca34, 0xfdbe51, 0xff5500, 0xffff68, 0xfb742f,
    0xbf7f3f, 0xff5555, 0xffe459, 0xef6f2f, 0xff2f1a, 0xffff8d, 0xffff99, 0xffd54f,
    0xffffcc, 0xff001c, 0xffcc66, 0xe28d38, 0xff3f3f, 0xff3f00, 0xffb624, 0x000000,
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
    0x000000, 0x000000, 0x000000, 0x000000, 0x000000, 0x000000, 0x000000, 0x000000,
    0x000000, 0x000000, 0x000000, 0x000000, 0x000000, 0x000000, 0x000000, 0x000000,
    0x000000, 0x000000, 0x000000, 0x000000, 0x000000, 0x000000, 0x000000, 0x000000,
    0x000000, 0x000000, 0x000000, 0x000000, 0x000000, 0x000000, 0x000000, 0x000000,
    0x000000, 0x000000, 0x000000, 0x000000, 0x000000, 0x000000, 0x000000, 0x000000,
    0x000000, 0x000000, 0x000000, 0x000000, 0x000000, 0x000000, 0x000000, 0x000000,
    0x000000, 0x000000, 0x000000, 0x000000, 0x000000, 0x000000, 0x000000, 0x000000,
    0x000000, 0x000000, 0x000000, 0x000000, 0x000000, 0x000000, 0x000000, 0x000000,
    0x000000, 0x000000, 0x000000, 0x000000, 0x000000, 0x000000, 0x000000, 0x000000
};
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
