whowechina/ju_pico/Matrix/firmware/src/res/marker13/mk0008_egg.h

#ifndef MK0008_EGG_C8_A8_H
#define MK0008_EGG_C8_A8_H

#include <stdint.h>

/* Marker definition macro */
#define DEF_mk0008_egg_c8_a8 { \
    .fps = 60, \
    { \
        { 8, 8, 13, 32, mk0008_egg_approach_pal8, mk0008_egg_approach_a8, .img8 = mk0008_egg_approach_pix8 }, \
        { 8, 8, 13, 32, mk0008_egg_perfect_pal8, mk0008_egg_perfect_a8, .img8 = mk0008_egg_perfect_pix8 }, \
        { 8, 8, 13, 32, mk0008_egg_great_pal8, mk0008_egg_great_a8, .img8 = mk0008_egg_great_pix8 }, \
        { 8, 8, 13, 32, mk0008_egg_good_pal8, mk0008_egg_good_a8, .img8 = mk0008_egg_good_pix8 }, \
        { 8, 8, 13, 32, mk0008_egg_poor_pal8, mk0008_egg_poor_a8, .img8 = mk0008_egg_poor_pix8 }, \
        { 8, 8, 13, 16, mk0008_egg_miss_pal8, mk0008_egg_miss_a8, .img8 = mk0008_egg_miss_pix8 } \
    } \
}

/* APPROACH - Using 8-bit color depth with 8-bit alpha */
const uint32_t mk0008_egg_approach_pal8[] = {
    0xdea15b, 0xe39b25, 0x625f21, 0xa7a357, 0xa35f1d, 0xdc6216, 0xa69c2b, 0x64a64d,
    0xdfd656, 0xa8d75a, 0x2c2a10, 0xf92610, 0x625f51, 0x2d9b33, 0x559428, 0xf3af92,
    0x71d34f, 0xe5e0db, 0xf2cca0, 0x562613, 0x9c7156, 0x2a5819, 0xb1d534, 0xdfcb1c,
    0x9b2903, 0xa8a6a0, 0xee7347, 0xff2cff, 0xf46aff, 0x1c5e5f, 0x0d1f46, 0xffa1ff,
    0x5dff90, 0x00ffff, 0xff007f, 0x3fdf7f, 0x550055, 0x55aaaa, 0xbdc6c8, 0x000000,
    0xfdfdfc, 0xfbfae8, 0xffff00, 0xfbfad9, 0x7e7e7e, 0x79aa37, 0x7e7e00, 0x699a29,
    0xff0000, 0x77a92d, 0x7ab437, 0x68a738, 0xc6f37a, 0xcaf684, 0xaaff55, 0x85b535,
    0x190702, 0x8ac956, 0xffff7f, 0xaaaa55, 0x756856, 0x6aa42b, 0x76b944, 0x00ff00,
    0x749a29, 0x94c53a, 0x48382a, 0x281709, 0xe8e5d7, 0xe8e6c6, 0x554738, 0xf67a25,
    0x9ad565, 0xe9e9e4, 0x867a66, 0xc9c3b8, 0xfa6807, 0xb5cc45, 0xc7ca46, 0x352517,
    0x665746, 0xe8e5b7, 0x958877, 0xf6f5c9, 0xc4bab4, 0xc3bb96, 0xaaaaaa, 0x759934,
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
